KozlovNikolai/manipulator/manipulyator/IMG_20190922_093729.jpg

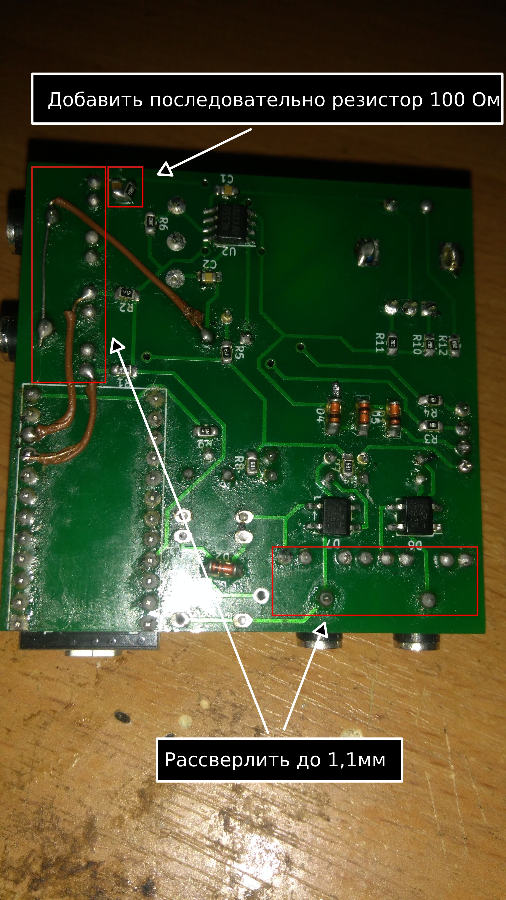
manipulyator/IMG_20190922_093729.jpg
