KozlovNikolai/manipulator/manipulyator/IMG_20190922_093738.jpg

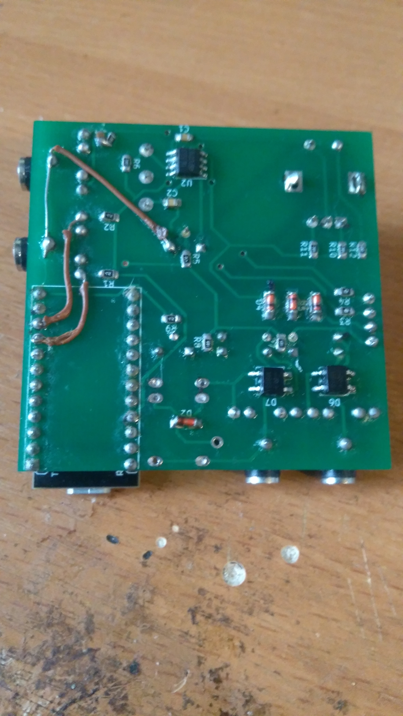
manipulyator/IMG_20190922_093738.jpg
