KozlovNikolai/manipulator/manipulyator/IMG_20190922_093827.jpg

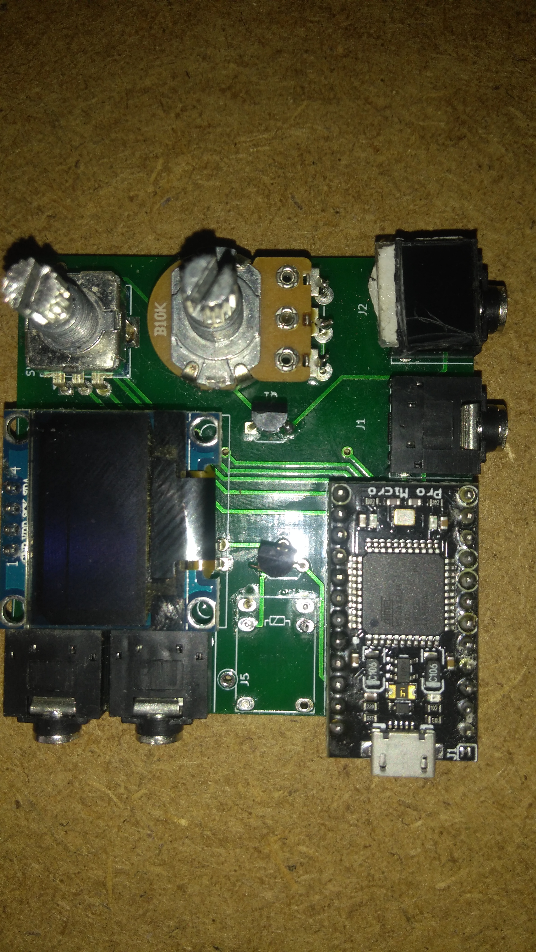
manipulyator/IMG_20190922_093827.jpg
