KozlovNikolai/manipulator/manipulyator/IMG_20190922_093832.jpg

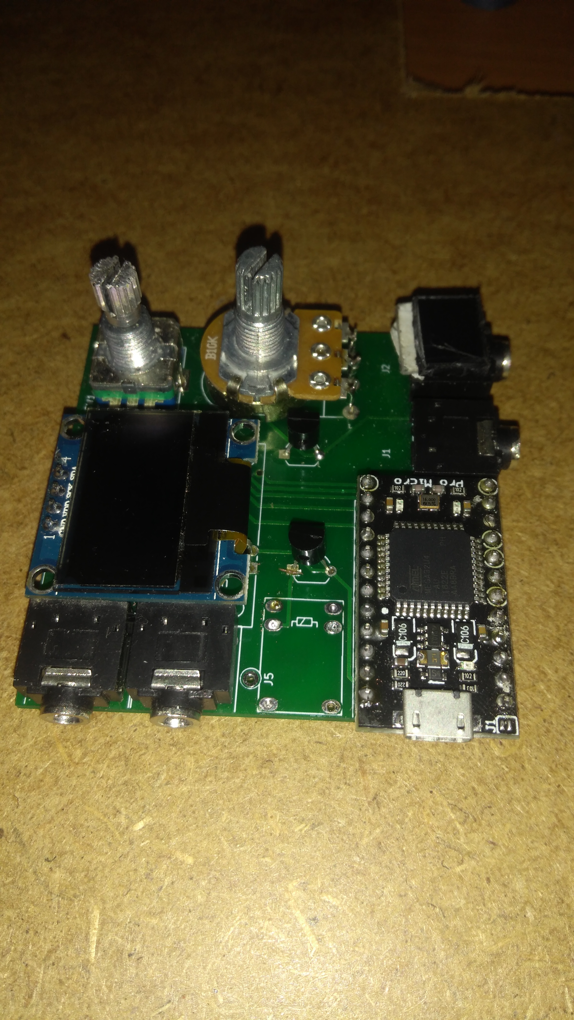
manipulyator/IMG_20190922_093832.jpg
