KozlovNikolai/manipulator/manipulyator/IMG_20190922_093840.jpg

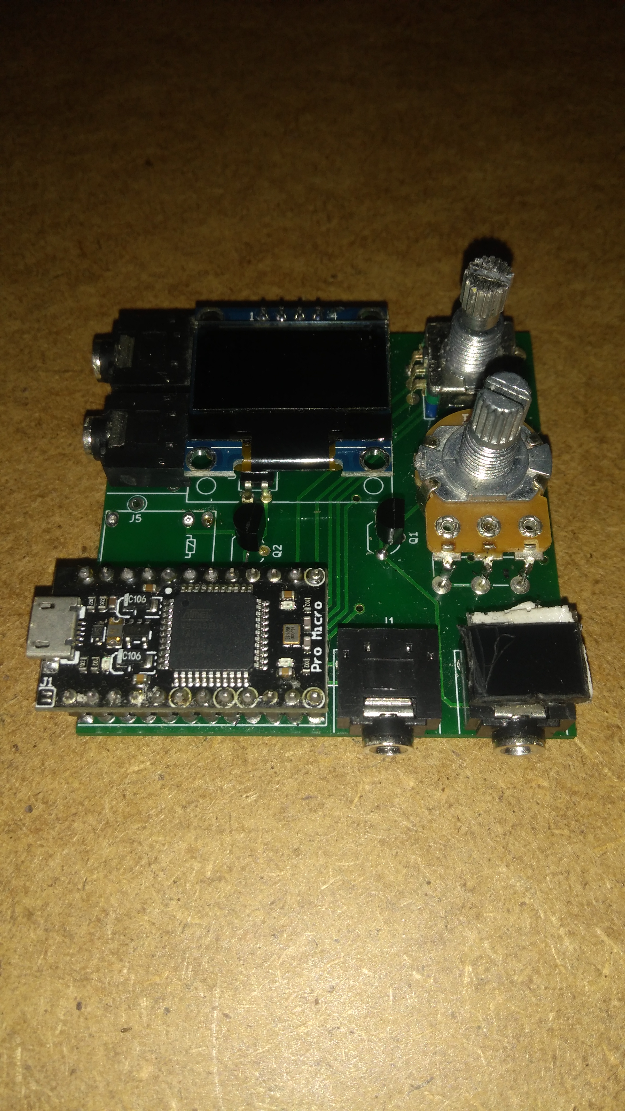
manipulyator/IMG_20190922_093840.jpg
