KozlovNikolai/manipulator/manipulyator/IMG_20190922_093853.jpg

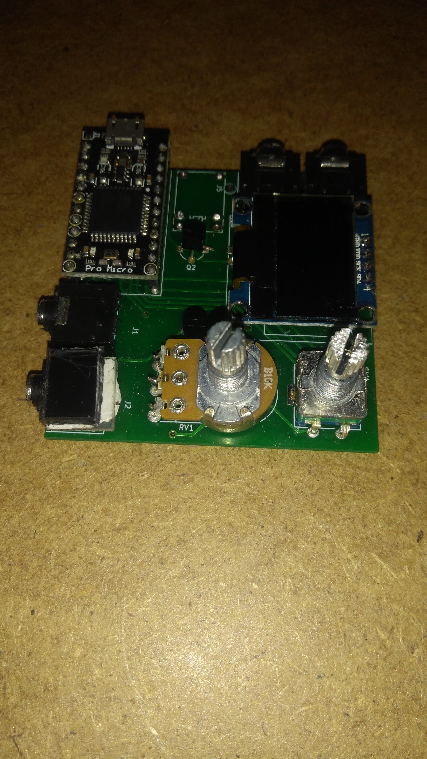
manipulyator/IMG_20190922_093853.jpg
