KozlovNikolai/manipulator/manipulyator/IMG_20190922_093904.jpg

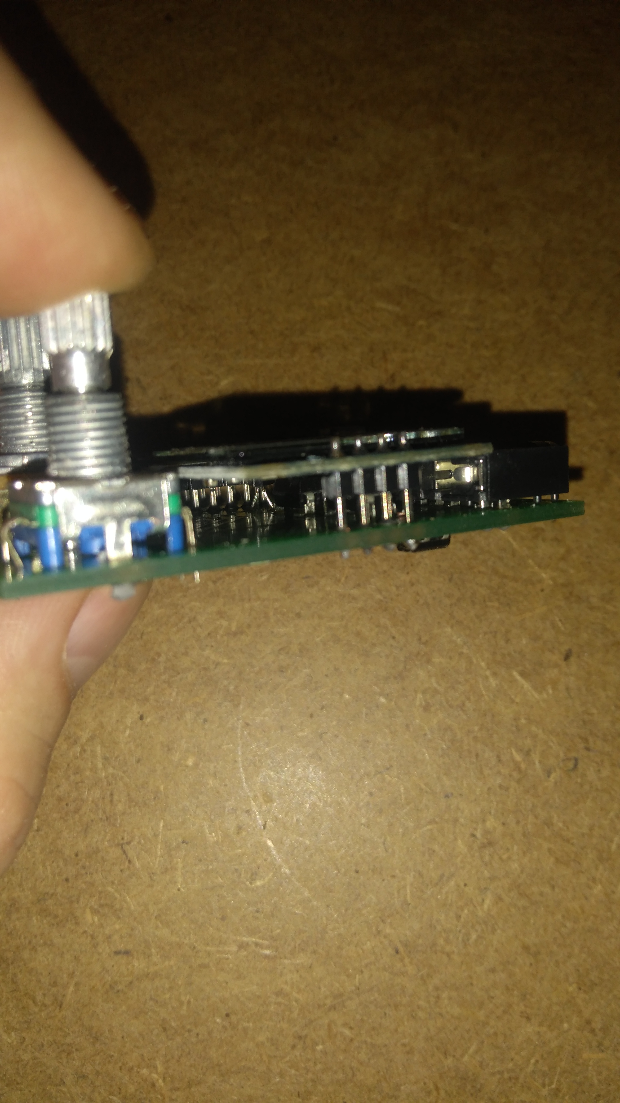
manipulyator/IMG_20190922_093904.jpg
