KozlovNikolai/manipulator/manipulyator/IMG_20190922_094056.jpg

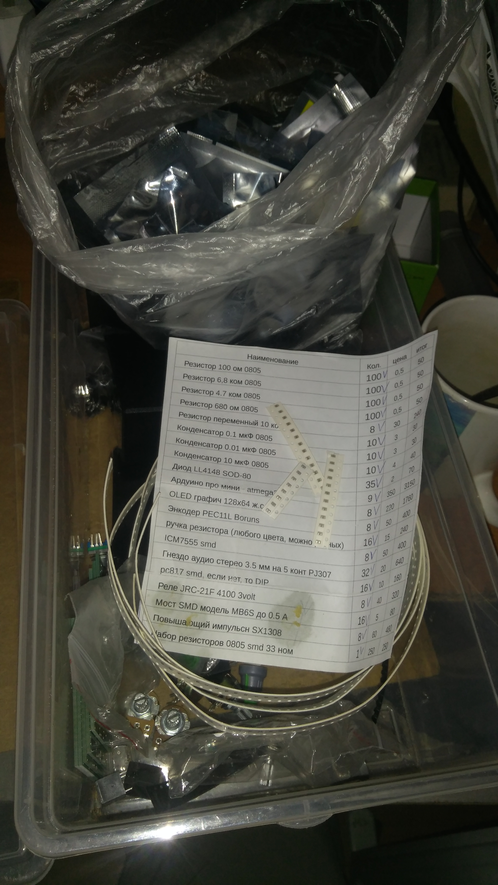
manipulyator/IMG_20190922_094056.jpg
