KozlovNikolai/manipulator/manipulyator/IMG_20190922_094111.jpg

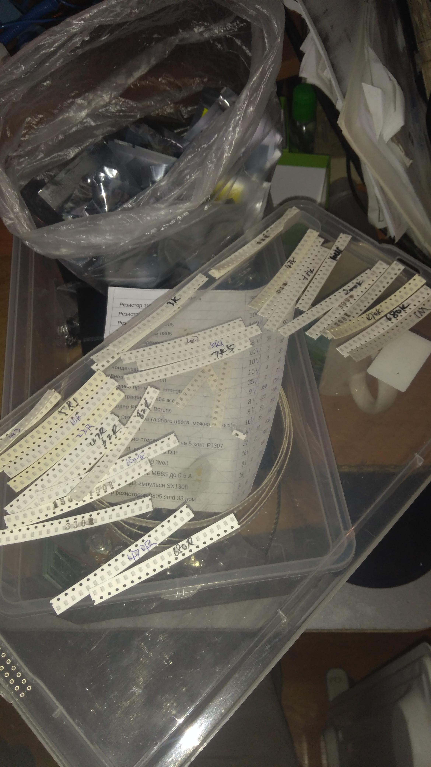
manipulyator/IMG_20190922_094111.jpg
