KozlovNikolai/manipulator/manipulyator/IMG_20190922_094119.jpg

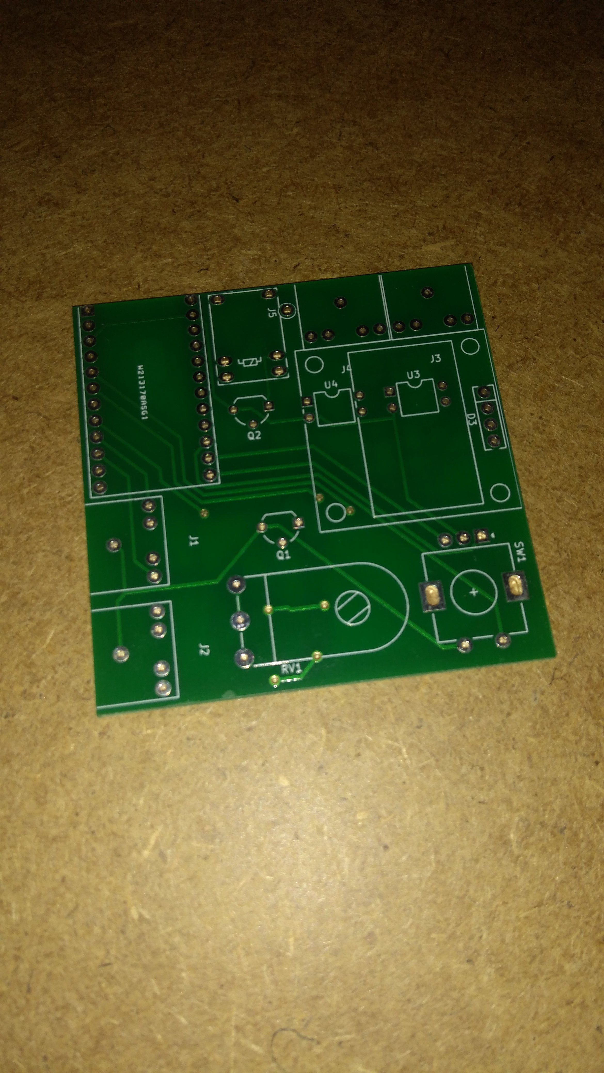
manipulyator/IMG_20190922_094119.jpg
