KozlovNikolai/manipulator/manipulyator/IMG_20190922_094126.jpg

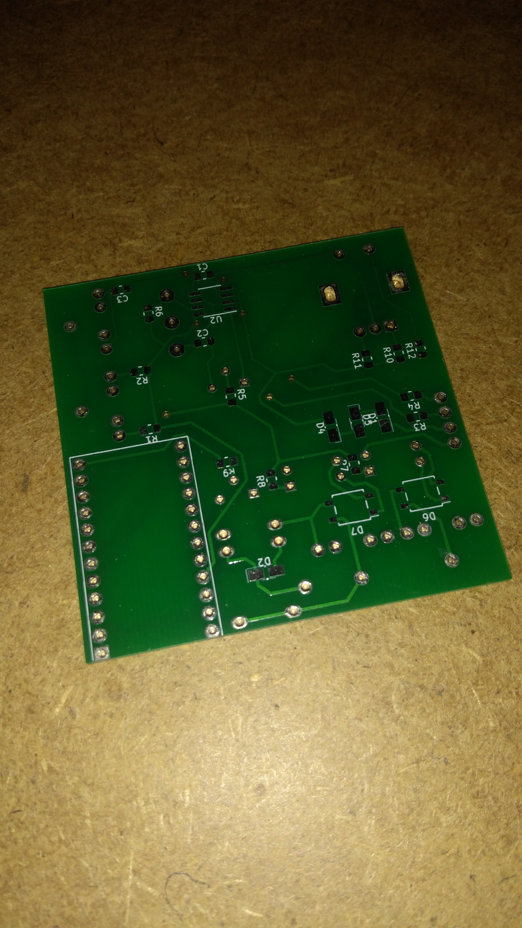
manipulyator/IMG_20190922_094126.jpg
