KozlovNikolai/manipulator/фото/IMG_20201106_203716_1.jpg

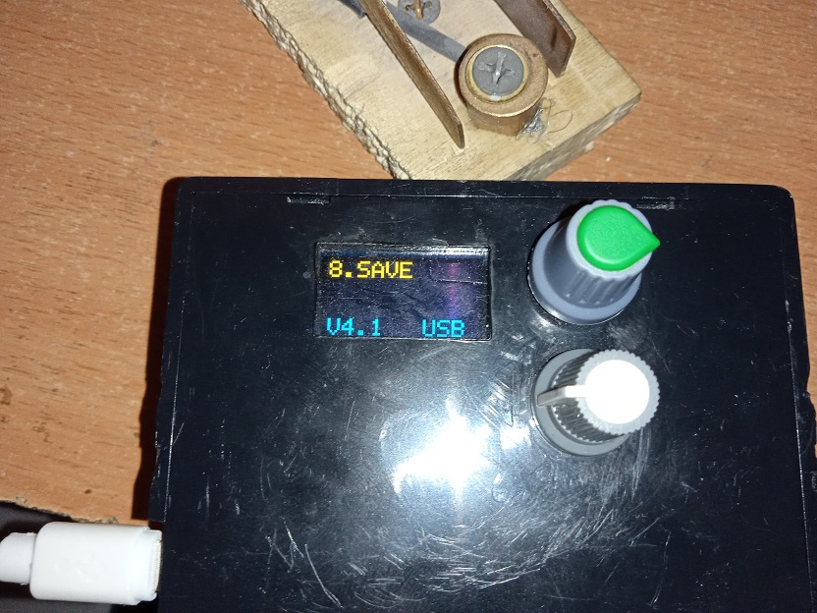
фото/IMG_20201106_203716_1.jpg
